adafruit/Adafruit-LPS2X-PCB/assets/4530.png

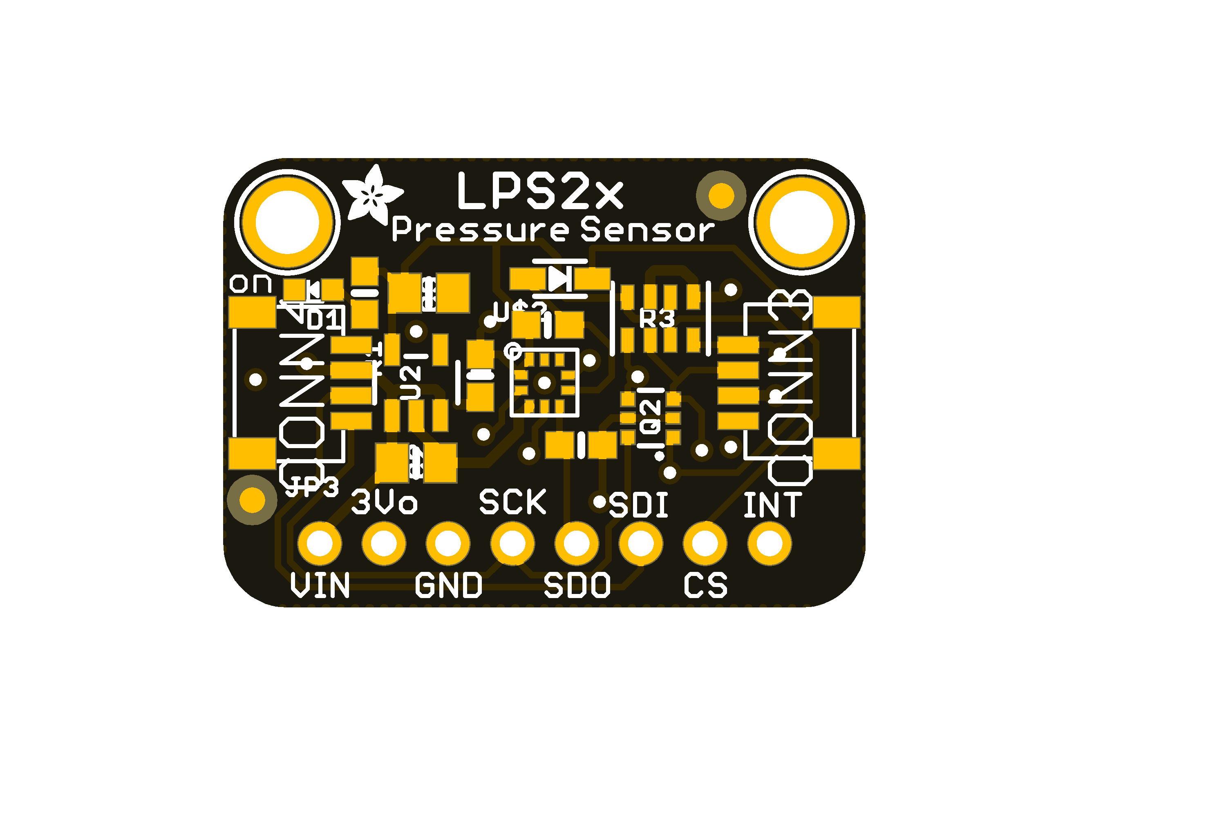
assets/4530.png
